nekrutnikolai/depth_sensor/pot_test/adc_log_2025-04-23_12-01-02.csv

timestamp_ms | ADC0 | ADC1 | ADC2
86 | 2085 | 2077 | 2052
182 | 2074 | 2072 | 2068
201 | 2093 | 2064 | 2053
210 | 2068 | 2066 | 2057
212 | 2073 | 2068 | 2052
212 | 2084 | 2069 | 2057
214 | 2090 | 2057 | 2065
214 | 2085 | 2052 | 2072
218 | 2093 | 2082 | 2068
219 | 2086 | 2075 | 2066
221 | 2072 | 2072 | 2054
222 | 2069 | 2075 | 2068
222 | 2082 | 2051 | 2065
224 | 2077 | 2068 | 2067
225 | 2076 | 2066 | 2064
225 | 2090 | 2070 | 2066
236 | 2091 | 2075 | 2062
250 | 2066 | 2075 | 2044
263 | 2085 | 2065 | 2067
277 | 2094 | 2052 | 2053
289 | 2071 | 2058 | 2070
302 | 2081 | 2080 | 2060
316 | 2090 | 2067 | 2059
329 | 2085 | 2077 | 2053
343 | 2077 | 2059 | 2052
355 | 2083 | 2076 | 2050
368 | 2077 | 2066 | 2069
382 | 2083 | 2067 | 2060
396 | 2064 | 2077 | 2067
409 | 2063 | 2050 | 2050
421 | 2081 | 2071 | 2070
435 | 2080 | 2073 | 2065
448 | 2083 | 2046 | 2062
462 | 2088 | 2068 | 2044
474 | 2073 | 2074 | 2050
487 | 2083 | 2066 | 2053
501 | 2087 | 2070 | 2060
514 | 2066 | 2069 | 2060
528 | 2092 | 2052 | 2050
540 | 2082 | 2075 | 2074
553 | 2074 | 2061 | 2059
567 | 2097 | 2053 | 2066
581 | 2076 | 2074 | 2068
594 | 2068 | 2081 | 2052
606 | 2066 | 2061 | 2055
620 | 2092 | 2054 | 2067
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
