nekrutnikolai/depth_sensor/pot_test/adc_log_2025-04-23_15-06-16.csv

timestamp_ms | ADC0 | ADC1 | ADC2
86 | 1730 | 1606 | 2009
178 | 1715 | 1603 | 2017
188 | 1720 | 1608 | 2010
197 | 1722 | 1595 | 2003
197 | 1722 | 1596 | 2002
198 | 1717 | 1594 | 1986
199 | 1716 | 1600 | 2010
200 | 1731 | 1615 | 1984
201 | 1736 | 1597 | 2013
218 | 1732 | 1610 | 2009
222 | 1734 | 1580 | 2004
222 | 1735 | 1612 | 2014
223 | 1717 | 1608 | 2009
224 | 1739 | 1600 | 2011
225 | 1723 | 1608 | 2011
226 | 1737 | 1610 | 2006
227 | 1723 | 1602 | 2014
232 | 1716 | 1612 | 1994
245 | 1733 | 1621 | 1994
258 | 1732 | 1609 | 2011
271 | 1737 | 1616 | 1986
285 | 1715 | 1613 | 1987
298 | 1734 | 1593 | 1995
310 | 1723 | 1611 | 1992
324 | 1713 | 1595 | 1992
337 | 1728 | 1598 | 2004
351 | 1723 | 1611 | 1994
364 | 1722 | 1602 | 2009
376 | 1728 | 1609 | 2002
390 | 1717 | 1603 | 2003
403 | 1728 | 1605 | 2008
417 | 1706 | 1598 | 1990
430 | 1712 | 1601 | 2012
443 | 1719 | 1610 | 2017
456 | 1733 | 1600 | 1999
470 | 1718 | 1610 | 2011
483 | 1732 | 1605 | 2008
495 | 1716 | 1606 | 1978
509 | 1737 | 1602 | 2015
522 | 1737 | 1613 | 2001
536 | 1728 | 1609 | 2010
549 | 1732 | 1618 | 2000
562 | 1722 | 1592 | 1996
575 | 1717 | 1608 | 2008
588 | 1739 | 1593 | 1993
602 | 1722 | 1593 | 1993
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
