nekrutnikolai/depth_sensor/pot_test/adc_log_2025-04-23_15-16-38.csv

timestamp_ms | ADC0 | ADC1 | ADC2
80 | 1403 | 1996 | 2040
172 | 1424 | 2003 | 2056
193 | 1414 | 2006 | 2036
195 | 1408 | 2010 | 2037
200 | 1417 | 2005 | 2049
202 | 1418 | 2001 | 2051
203 | 1427 | 1995 | 2059
204 | 1409 | 1988 | 2054
205 | 1403 | 2008 | 2045
206 | 1417 | 2005 | 2061
207 | 1420 | 2005 | 2044
208 | 1409 | 1996 | 2050
209 | 1405 | 2004 | 2037
210 | 1427 | 1991 | 2035
211 | 1405 | 2009 | 2053
212 | 1421 | 1997 | 2055
220 | 1403 | 1996 | 2054
232 | 1405 | 2001 | 2054
246 | 1411 | 1980 | 2034
259 | 1419 | 1993 | 2050
273 | 1414 | 1993 | 2052
286 | 1412 | 2001 | 2030
298 | 1415 | 1990 | 2052
312 | 1413 | 2004 | 2025
326 | 1413 | 2000 | 2052
339 | 1408 | 1995 | 2057
352 | 1403 | 2002 | 2040
364 | 1401 | 1995 | 2058
378 | 1420 | 2008 | 2061
392 | 1404 | 1996 | 2053
405 | 1410 | 1984 | 2055
417 | 1405 | 2002 | 2058
431 | 1406 | 2000 | 2042
444 | 1416 | 2002 | 2040
458 | 1413 | 1993 | 2052
471 | 1402 | 1985 | 2041
483 | 1405 | 1984 | 2049
497 | 1411 | 1995 | 2040
510 | 1415 | 1982 | 2043
524 | 1406 | 2004 | 2048
537 | 1421 | 2007 | 2052
549 | 1406 | 1992 | 2027
563 | 1423 | 2002 | 2060
577 | 1420 | 2002 | 2051
590 | 1426 | 2005 | 2053
602 | 1420 | 1981 | 2052
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
