nekrutnikolai/depth_sensor/pot_test/adc_log_2025-04-23_15-19-28.csv

timestamp_ms | ADC0 | ADC1 | ADC2
81 | 1392 | 1998 | 2063
171 | 1409 | 1998 | 2045
194 | 1398 | 2005 | 2044
195 | 1406 | 2009 | 2064
196 | 1390 | 1989 | 2044
197 | 1390 | 1994 | 2060
198 | 1404 | 1986 | 2059
199 | 1401 | 1994 | 2051
200 | 1401 | 1993 | 2058
201 | 1410 | 1977 | 2050
202 | 1389 | 2006 | 2044
203 | 1403 | 2005 | 2051
204 | 1396 | 1992 | 2057
209 | 1399 | 1985 | 2056
210 | 1400 | 1994 | 2040
211 | 1410 | 1993 | 2037
217 | 1406 | 2005 | 2045
231 | 1402 | 1998 | 2042
244 | 1411 | 2003 | 2054
258 | 1397 | 2001 | 2039
270 | 1400 | 1997 | 2040
284 | 1392 | 2000 | 2058
297 | 1396 | 1988 | 2045
310 | 1402 | 1981 | 2060
322 | 1396 | 2004 | 2061
336 | 1397 | 1996 | 2059
349 | 1405 | 1985 | 2050
363 | 1404 | 1987 | 2054
377 | 1385 | 1996 | 2049
389 | 1401 | 1993 | 2034
402 | 1398 | 2004 | 2027
416 | 1400 | 1999 | 2032
429 | 1386 | 1991 | 2057
443 | 1396 | 2010 | 2052
455 | 1416 | 2005 | 2050
468 | 1402 | 1993 | 2045
482 | 1400 | 1998 | 2058
496 | 1400 | 1983 | 2049
509 | 1401 | 1982 | 2050
521 | 1396 | 2002 | 2028
534 | 1408 | 1999 | 2044
548 | 1388 | 1990 | 2041
562 | 1398 | 1997 | 2027
574 | 1408 | 1981 | 2057
587 | 1393 | 1989 | 2049
601 | 1396 | 1999 | 2042
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
